Leonie-Winter/MORRIGAN/theorethical_work/figures/JugendForscht_figures/diagramm_1_MORRIGAN.png

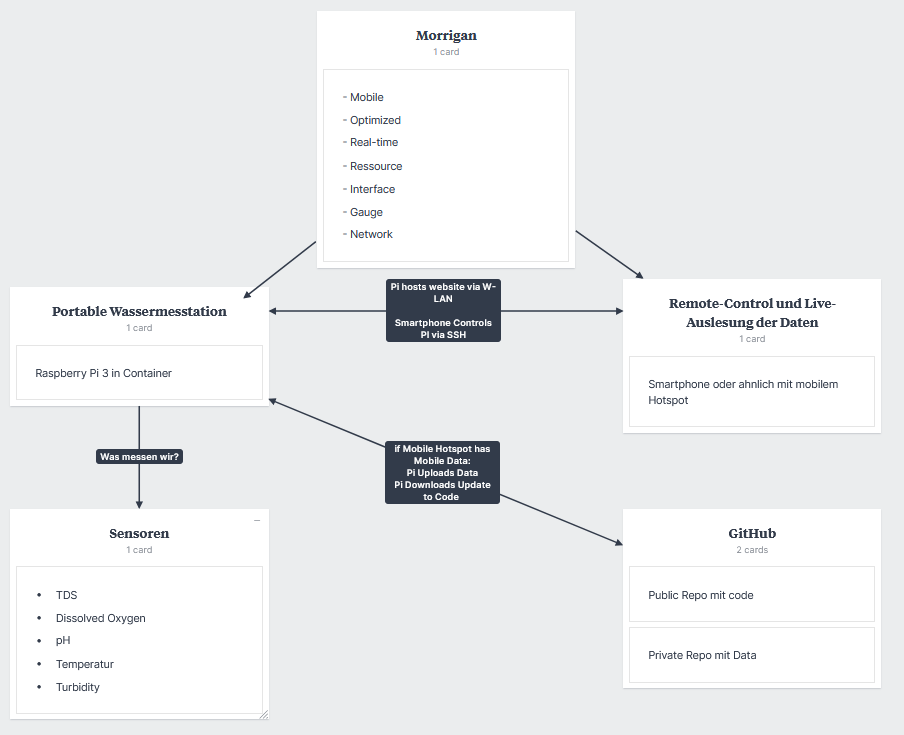
theorethical_work/figures/JugendForscht_figures/diagramm_1_MORRIGAN.png
