Leonie-Winter/MORRIGAN/theorethical_work/figures/JugendForscht_figures/diagramm_2_expandability.png

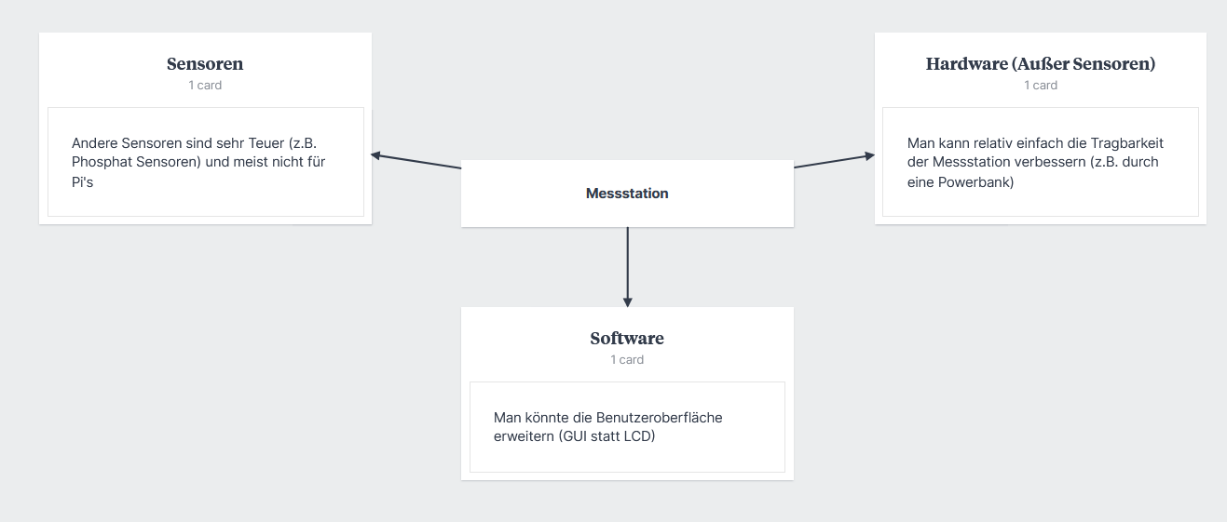
theorethical_work/figures/JugendForscht_figures/diagramm_2_expandability.png
