Leonie-Winter/MORRIGAN/theorethical_work/figures/MORRIGAN_figures/figure_3_amplitude_modulated_vs_frequency_modulated.png

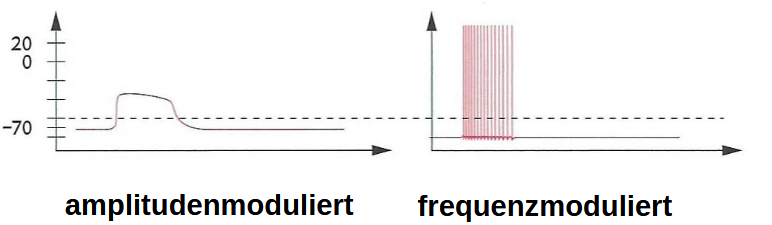
theorethical_work/figures/MORRIGAN_figures/figure_3_amplitude_modulated_vs_frequency_modulated.png
