Leonie-Winter/MORRIGAN/theorethical_work/figures/MORRIGAN_figures/figure_5_pcb_of_pi_hat.png

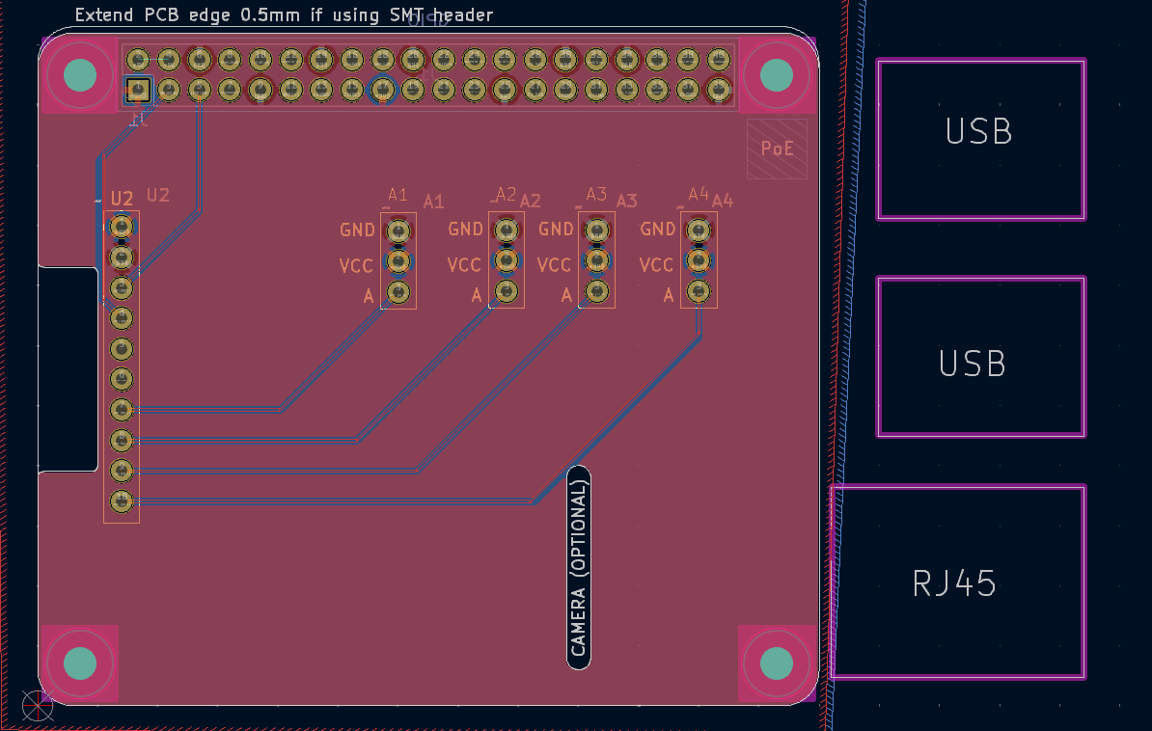
theorethical_work/figures/MORRIGAN_figures/figure_5_pcb_of_pi_hat.png
