Leonie-Winter/MORRIGAN/theorethical_work/figures/MORRIGAN_figures/figure_6_circuit_diagram_of_pi_hat.png

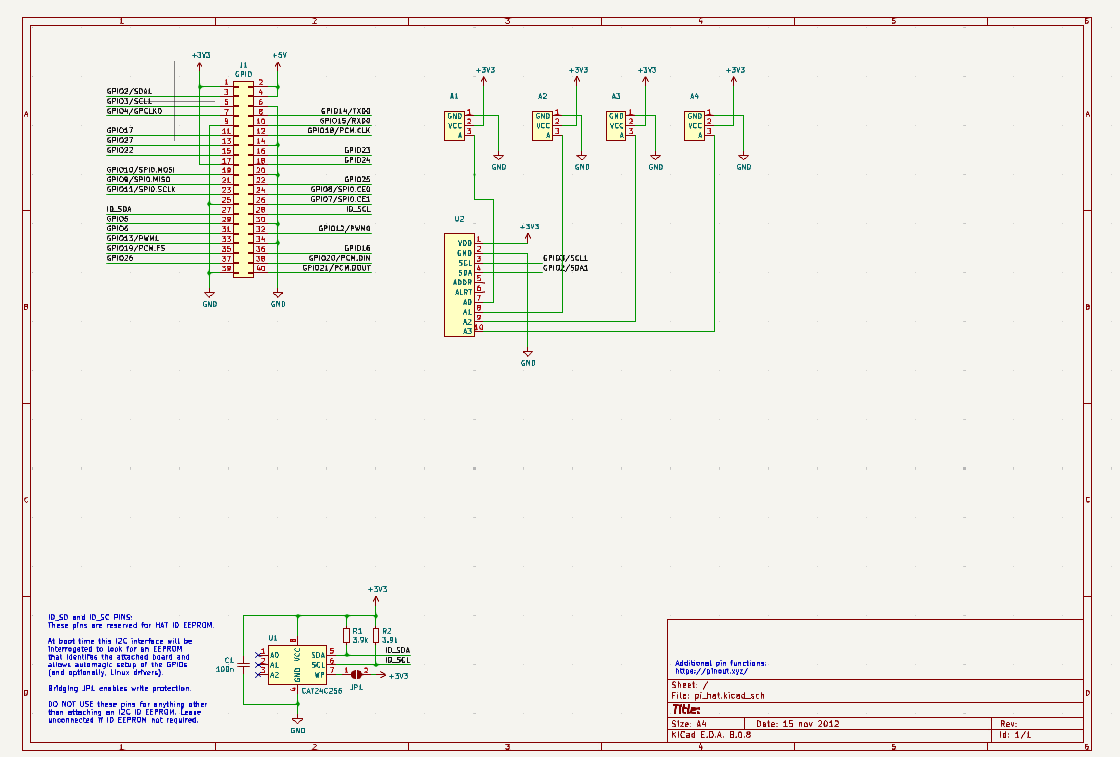
theorethical_work/figures/MORRIGAN_figures/figure_6_circuit_diagram_of_pi_hat.png
