Leonie-Winter/MORRIGAN/theorethical_work/figures/MORRIGAN_figures/figure_7_pi_hat_in_fritzing.png

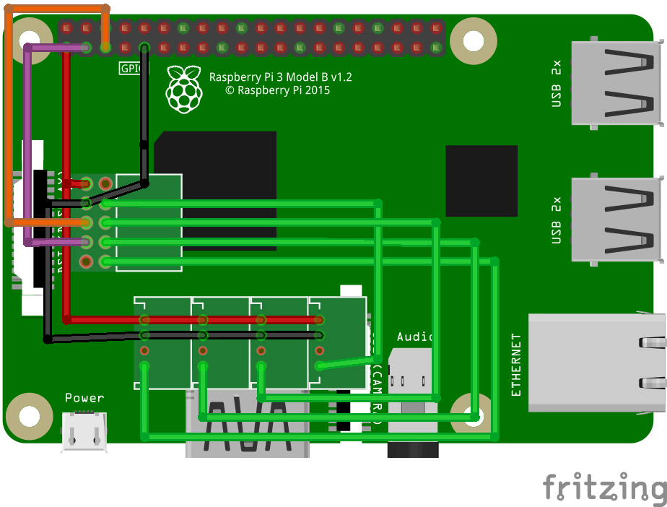
theorethical_work/figures/MORRIGAN_figures/figure_7_pi_hat_in_fritzing.png
