Leonie-Winter/MORRIGAN/theorethical_work/figures/MORRIGAN_figures/figure_10_ph_sensor_with_breadboard.png

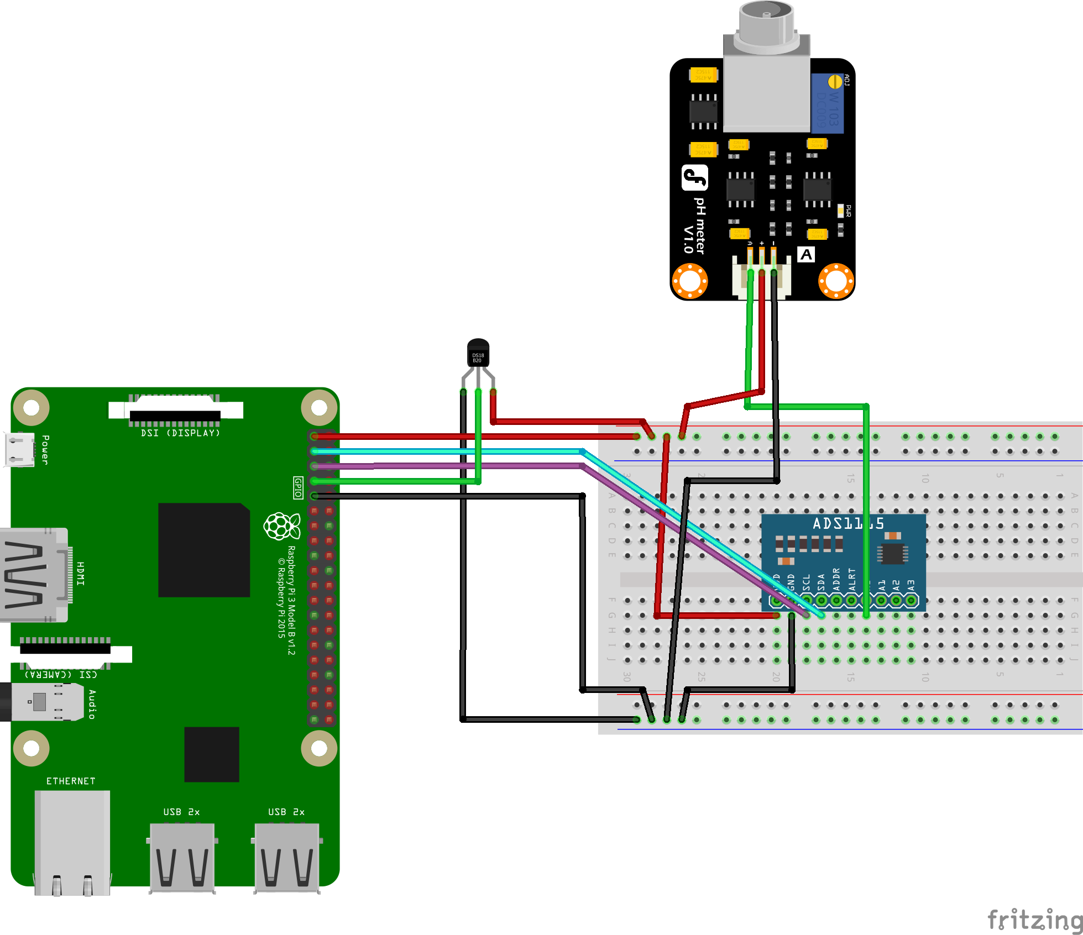
theorethical_work/figures/MORRIGAN_figures/figure_10_ph_sensor_with_breadboard.png
