Leonie-Winter/MORRIGAN/theorethical_work/figures/MORRIGAN_figures/figure_11_ph_sensor_with_pcb.png

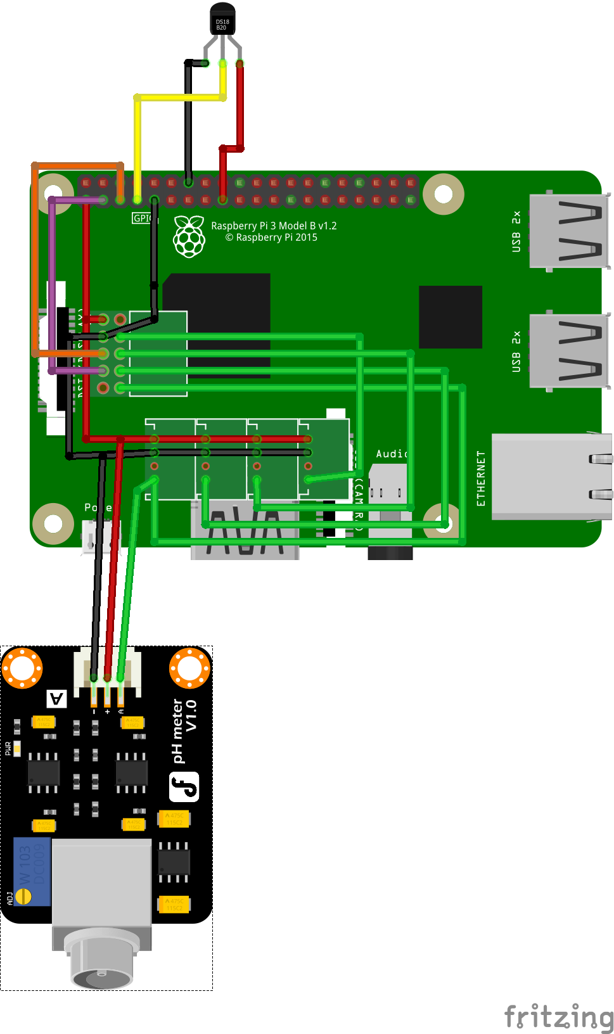
theorethical_work/figures/MORRIGAN_figures/figure_11_ph_sensor_with_pcb.png
