Leonie-Winter/MORRIGAN/theorethical_work/figures/MORRIGAN_figures/figure_13_tds_sensor_with_breadboard.png

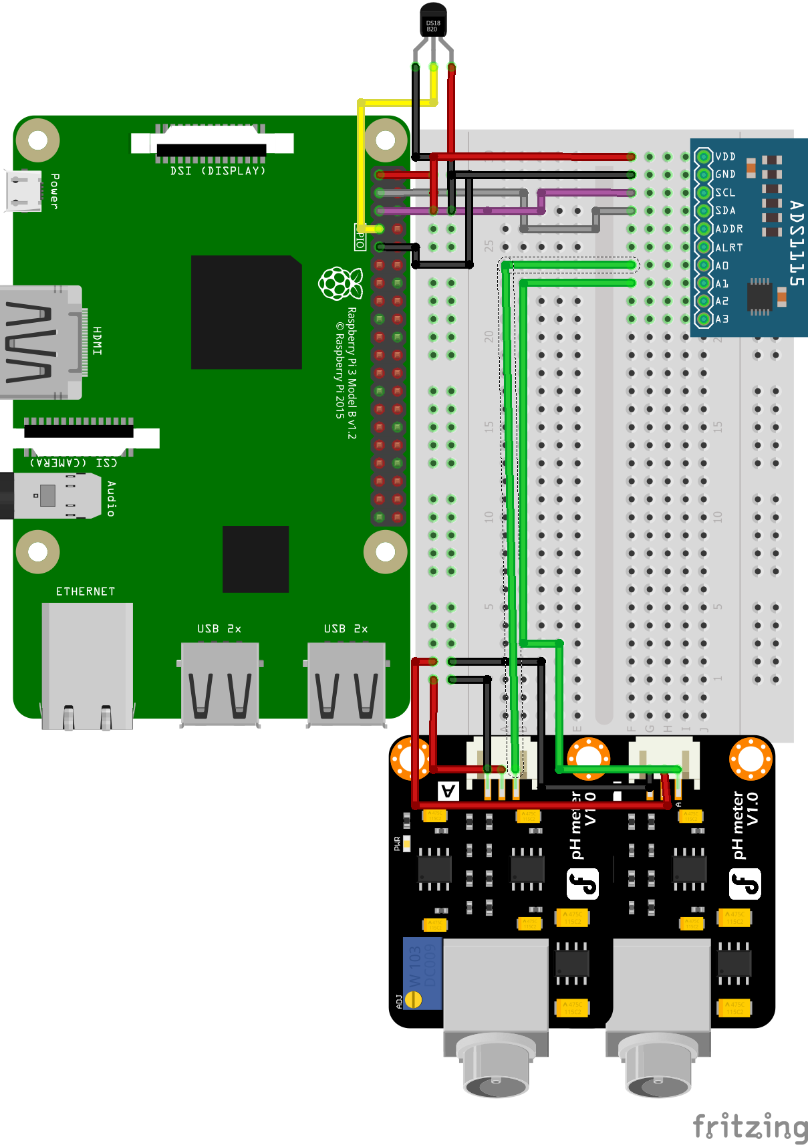
theorethical_work/figures/MORRIGAN_figures/figure_13_tds_sensor_with_breadboard.png
