Leonie-Winter/MORRIGAN/theorethical_work/figures/MORRIGAN_figures/figure_14_ec_graph.png

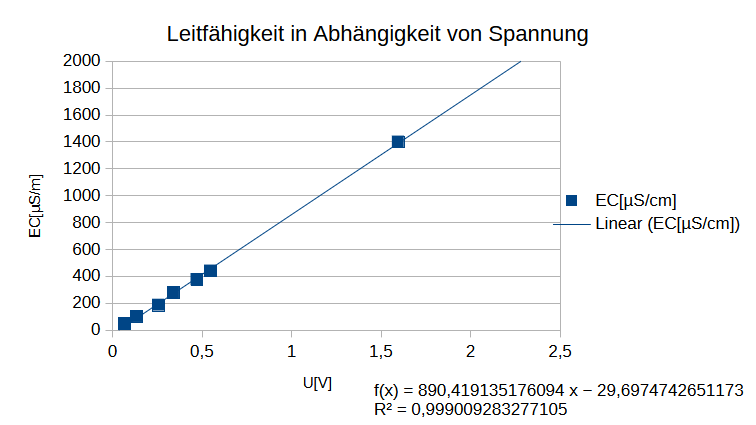
theorethical_work/figures/MORRIGAN_figures/figure_14_ec_graph.png
