Leonie-Winter/MORRIGAN/theorethical_work/figures/MORRIGAN_figures/figure_17_do_graph.png

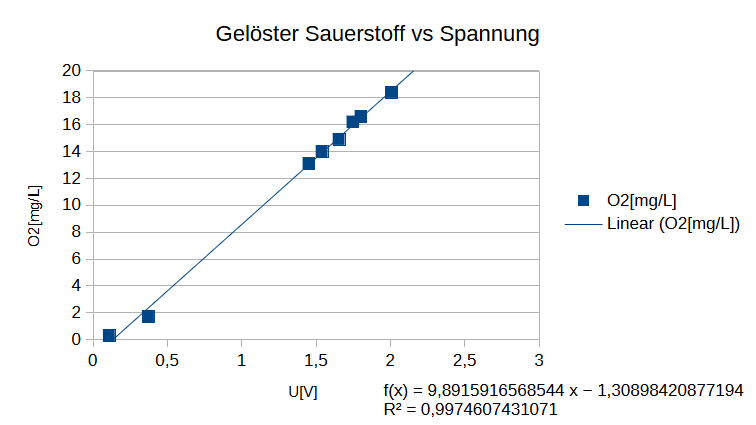
theorethical_work/figures/MORRIGAN_figures/figure_17_do_graph.png
