Leonie-Winter/MORRIGAN/theorethical_work/figures/MORRIGAN_figures/figure_18_do_vs_temp_graph.png

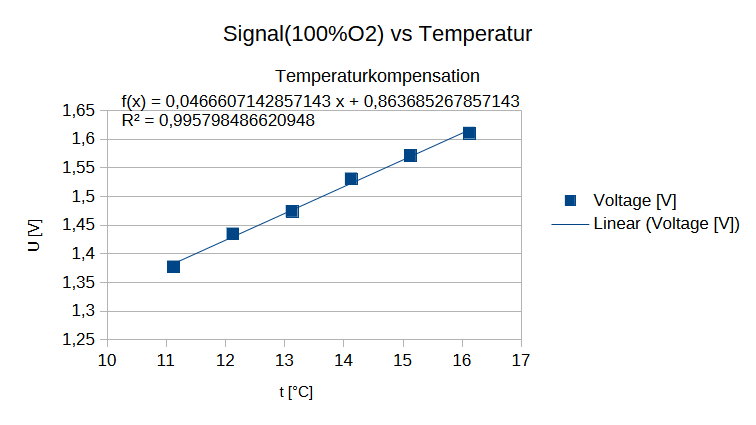
theorethical_work/figures/MORRIGAN_figures/figure_18_do_vs_temp_graph.png
