Leonie-Winter/MORRIGAN/theorethical_work/figures/MORRIGAN_figures/figure_21_turbidity_graph.png

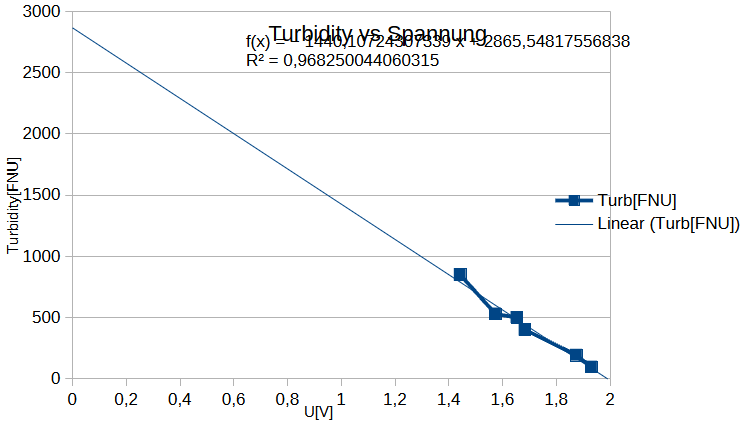
theorethical_work/figures/MORRIGAN_figures/figure_21_turbidity_graph.png
