Leonie-Winter/MORRIGAN/theorethical_work/figures/MORRIGAN_figures/figure_22_the_3d_modell.png

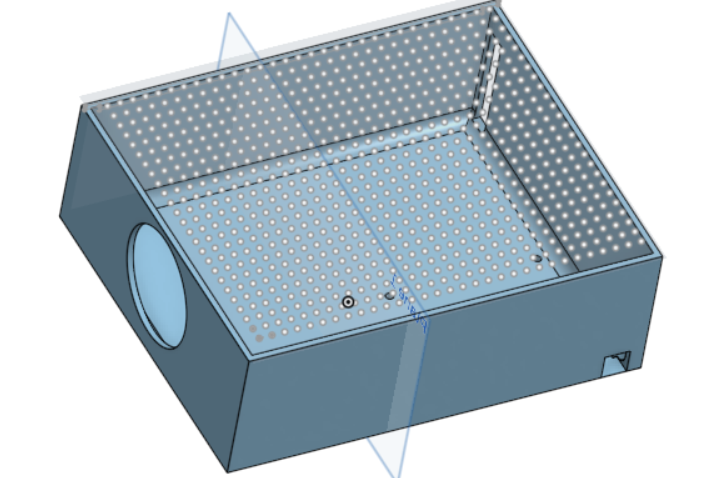
theorethical_work/figures/MORRIGAN_figures/figure_22_the_3d_modell.png
