Leonie-Winter/MORRIGAN/theorethical_work/figures/poster_figures/simple_raspberry.png

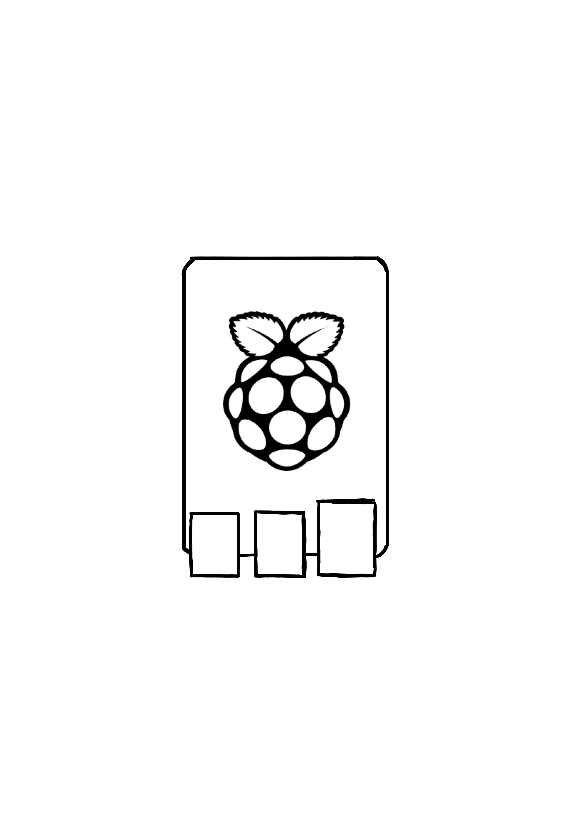
theorethical_work/figures/poster_figures/simple_raspberry.png
