Leonie-Winter/MORRIGAN/theorethical_work/figures/poster_figures/simple_sensor.png

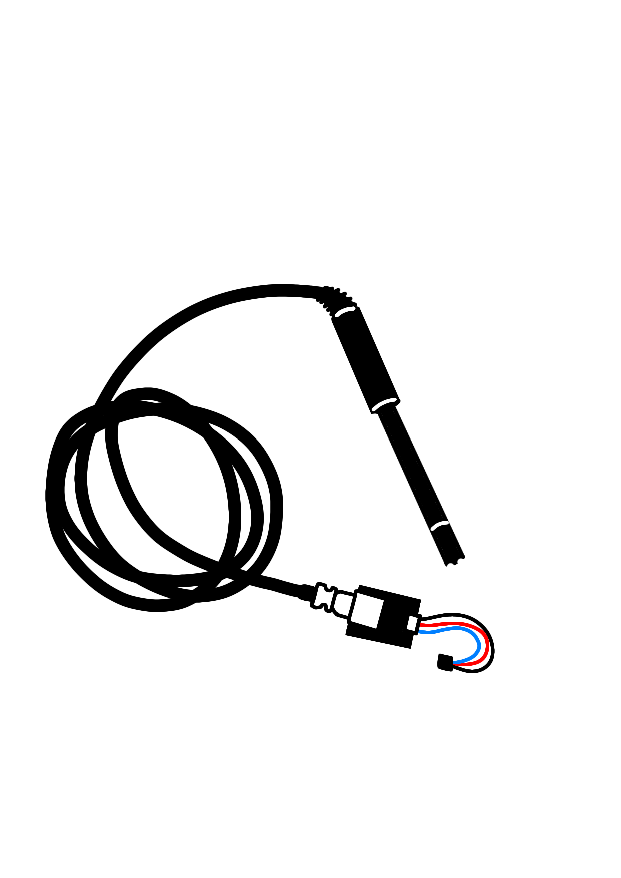
theorethical_work/figures/poster_figures/simple_sensor.png
