Leonie-Winter/MORRIGAN/theorethical_work/figures/poster_figures/white_flyingfish_simple_l.png

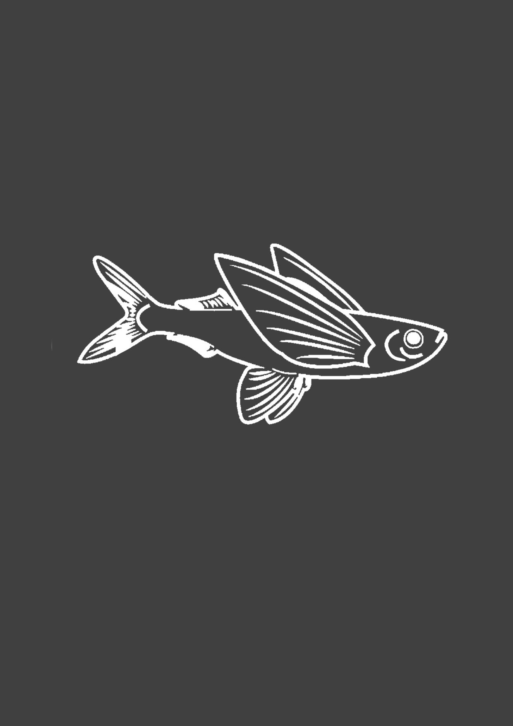
theorethical_work/figures/poster_figures/white_flyingfish_simple_l.png
