Leonie-Winter/MORRIGAN/theorethical_work/figures/poster_figures/white_swordfish_simple_r.png

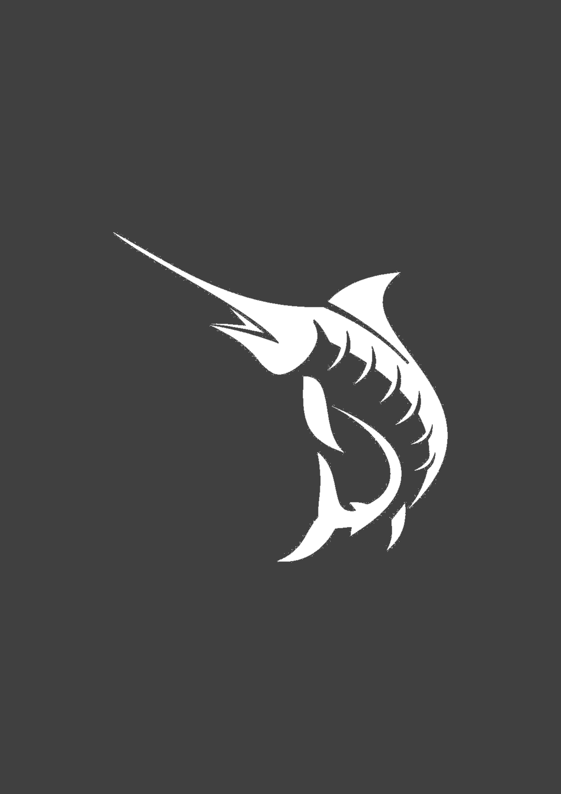
theorethical_work/figures/poster_figures/white_swordfish_simple_r.png
