Leonie-Winter/MORRIGAN/theorethical_work/figures/MORRIGAN_figures/figure_4_wiring_of_ads1115_with_pi.png

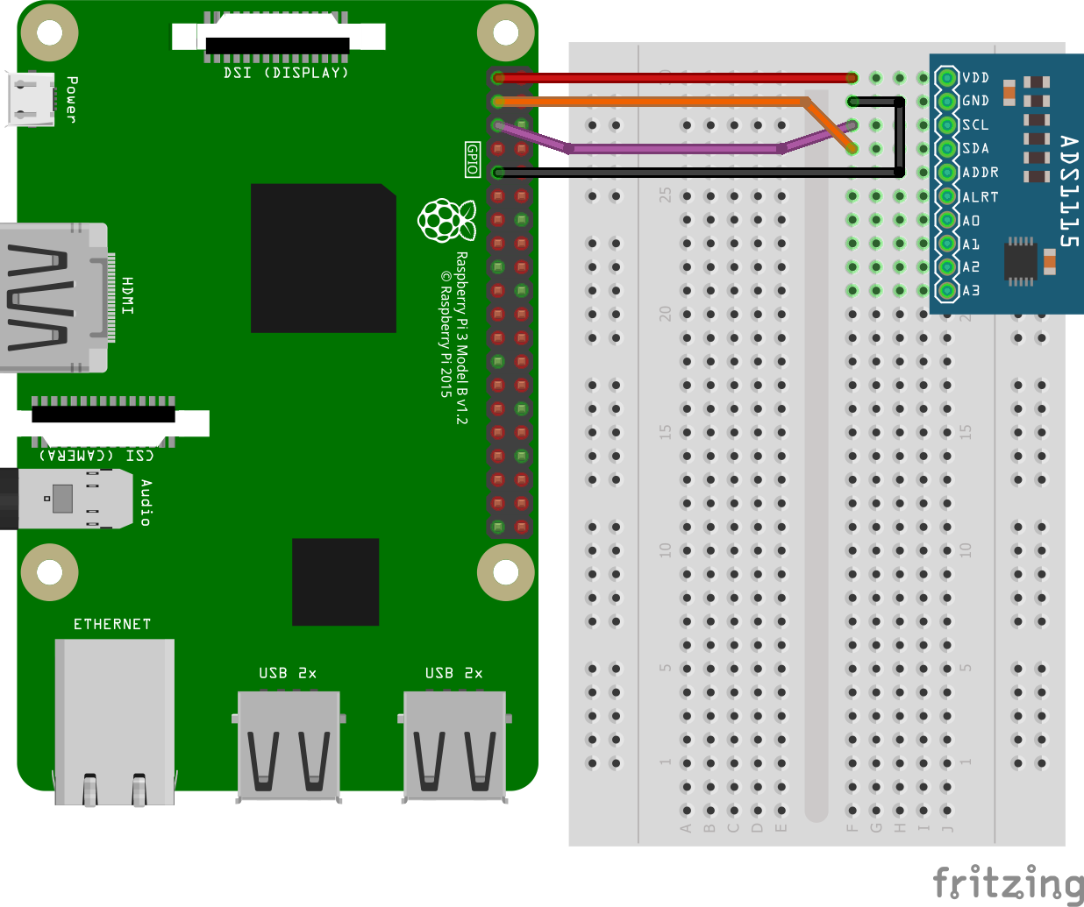
theorethical_work/figures/MORRIGAN_figures/figure_4_wiring_of_ads1115_with_pi.png
