Leonie-Winter/MORRIGAN/src/backend/sensors/test2.py

import board, time, busio, os, glob, adafruit_ads1x15.ads1115 as ADS
from adafruit_ads1x15.analog_in import AnalogIn

i2c = busio.I2C(board.SCL, board.SDA)
ads = ADS.ADS1115(i2c)
ads.gain = 2
channel0 = AnalogIn(ads, ADS.P0)
channel1 = AnalogIn(ads, ADS.P1)
os.system('modprobe w1-gpio')
os.system('modprobe w1-therm')
base_dir = '/sys/bus/w1/devices/'
device_folder = glob.glob(base_dir + '28*')[0]
device_file = device_folder + '/w1_slave'
def read_temp_raw():
    f = open(device_file, 'r')
    lines = f.readlines()
    f.close()
    return lines
def read_temp():
    lines = read_temp_raw()
    while lines[0].strip()[-3:] != 'YES':
        time.sleep(0.2)
        lines = read_temp_raw()
    equals_pos = lines[1].find('t=')
    if equals_pos != -1:
        temp_string = lines[1][equals_pos+2:]
        temp_c = float(temp_string) / 1000.0
        temp_f = temp_c * 9.0 / 5.0 + 32.0
        return temp_c, temp_f

while True:
    print("Analog Value 0: ", channel0.value, "Voltage 0: ", channel0.voltage)
    print("Analog Value 1: ", channel1.value, "Voltage 1: ", channel1.voltage)
    print(read_temp())
    # Delay for 1 second
    time.sleep(1)
